Heymann03/wireless_sensor_measurement/Source_Code/BLE_ESP32.ino

#include <BLEDevice.h>
#include <BLEServer.h>
#include <BLEUtils.h>
#include <BLE2902.h>


BLECharacteristic *pCharacteristic;
bool deviceConnected = false;
int txValue = 0;

#define SERVICE_UUID "6E400001-B5A3-F393-E0A9-E50E24DCCA9E"
#define CHARACTERISTIC_UUID_TX "6E400002-B5A3-F393-E0A9-E50E24DCCA9E"
#define CHARACTERISTIC_UUID_RX "6E400003-B5A3-F393-E0A9-E50E24DCCA9E"

class MyServerCallbacks: public BLEServerCallbacks {
  void onConnect(BLEServer* pServer){
    deviceConnected = true;
  };

  void onDisconnect(BLEServer* pServer){
    deviceConnected = false;
  }
};

 class MyCallbacks: public BLECharacteristicCallbacks{
  void onWrite(BLECharacteristic *pCharacteristic){
    std::string rxValue = pCharacteristic->getValue(); 
  }
 };
void setup() {
  // put your setup code here, to run once:
   Serial.begin(9600);
   Serial.println("start here"); 
   
   //create the BLE Device
   BLEDevice::init("ESP32");//Give it a name

   //Create BLE Server
   BLEServer *pServer = BLEDevice::createServer();
   pServer->setCallbacks(new MyServerCallbacks());

   //Create the BLE Service
   BLEService *pService = pServer->createService(SERVICE_UUID);

   //Create a BLE Characteristic_tx
   pCharacteristic = pService->createCharacteristic(
                      CHARACTERISTIC_UUID_TX,
                      BLECharacteristic::PROPERTY_NOTIFY
                      );
                      
  //BLE2902 needed to notify
  pCharacteristic->addDescriptor(new BLE2902());

  //Create characteristic_rx
     BLECharacteristic *pCharacteristic = pService->createCharacteristic(
                                         CHARACTERISTIC_UUID_RX,
                                         BLECharacteristic::PROPERTY_WRITE
                                       );

 pCharacteristic->setCallbacks(new MyCallbacks());
  
  //start the service
  pService->start();

  //Start advertising
  pServer->getAdvertising()->start();
  Serial.println("Waiting for a client connection to notify...");
}
void loop() {
  // put your main code here, to run repeatedly:

   if (deviceConnected){
    txValue = random(-10, 20);

    //conversion of txValue
    char txString[8];
    dtostrf(txValue, 1, 2, txString);

    //setting the value to the characteristic
    pCharacteristic->setValue(txString);

    //Notifying the connected client
    pCharacteristic->notify();
    Serial.println("Sent value: " + String(txString));
    delay(1000);
   }
}
